DrMikeG/H2Remote/readme_img/h4remote.jpg

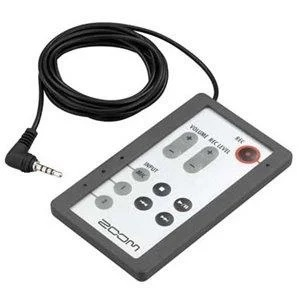
readme_img/h4remote.jpg
