DrMikeG/H2Remote/readme_img/pico01.jpg

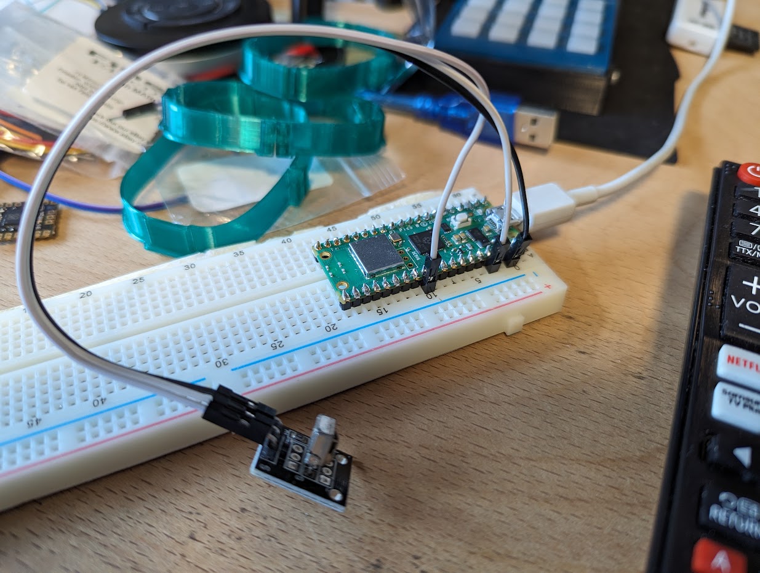
readme_img/pico01.jpg
