DrMikeG/H2Remote/readme_img/tiny_led_pins.png

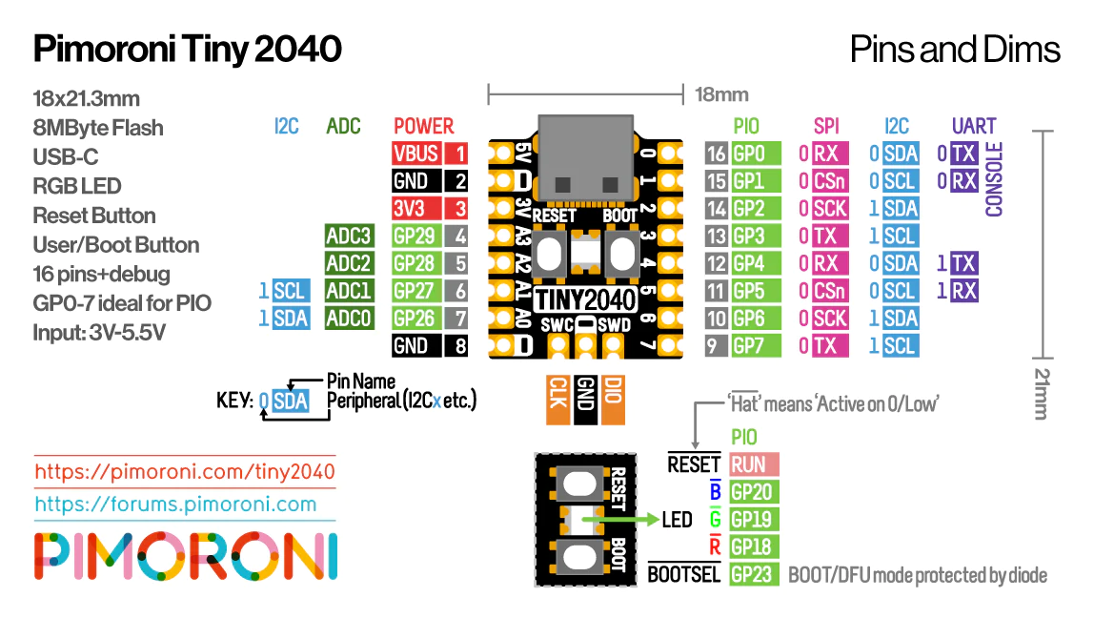
readme_img/tiny_led_pins.png
