DrMikeG/H2Remote/timelapse/pi3/Raspberry_Pi_7_Inch_Touchscreen_display_case_1585924/images/Raspi7inch_Split_Left_Case_SD_Access.jpg

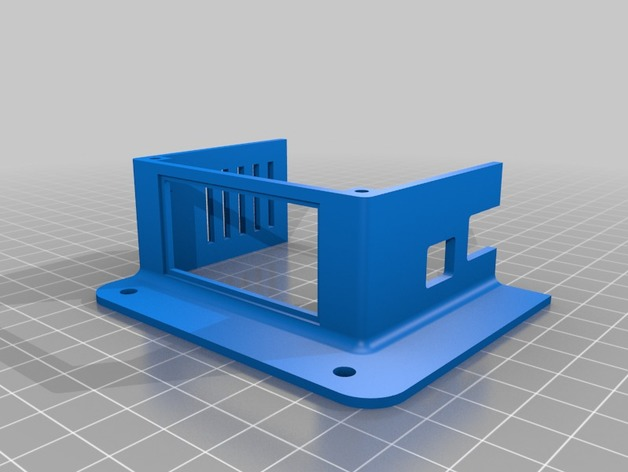
timelapse/pi3/Raspberry_Pi_7_Inch_Touchscreen_display_case_1585924/images/Raspi7inch_Split_Left_Case_SD_Access.jpg
