DrMikeG/H2Remote/Updates/Update1/00_Instant.png

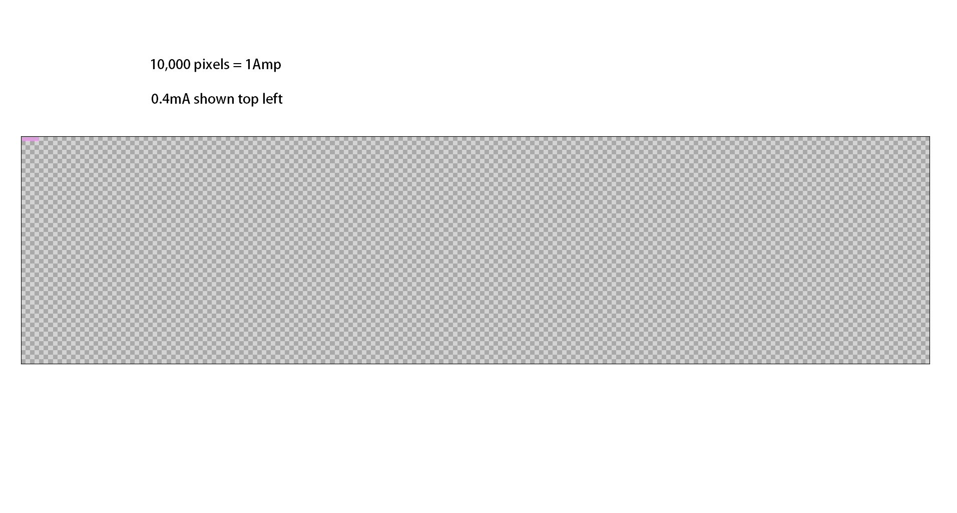
Updates/Update1/00_Instant.png
