DrMikeG/H2Remote/Updates/Update1/02_aas.png

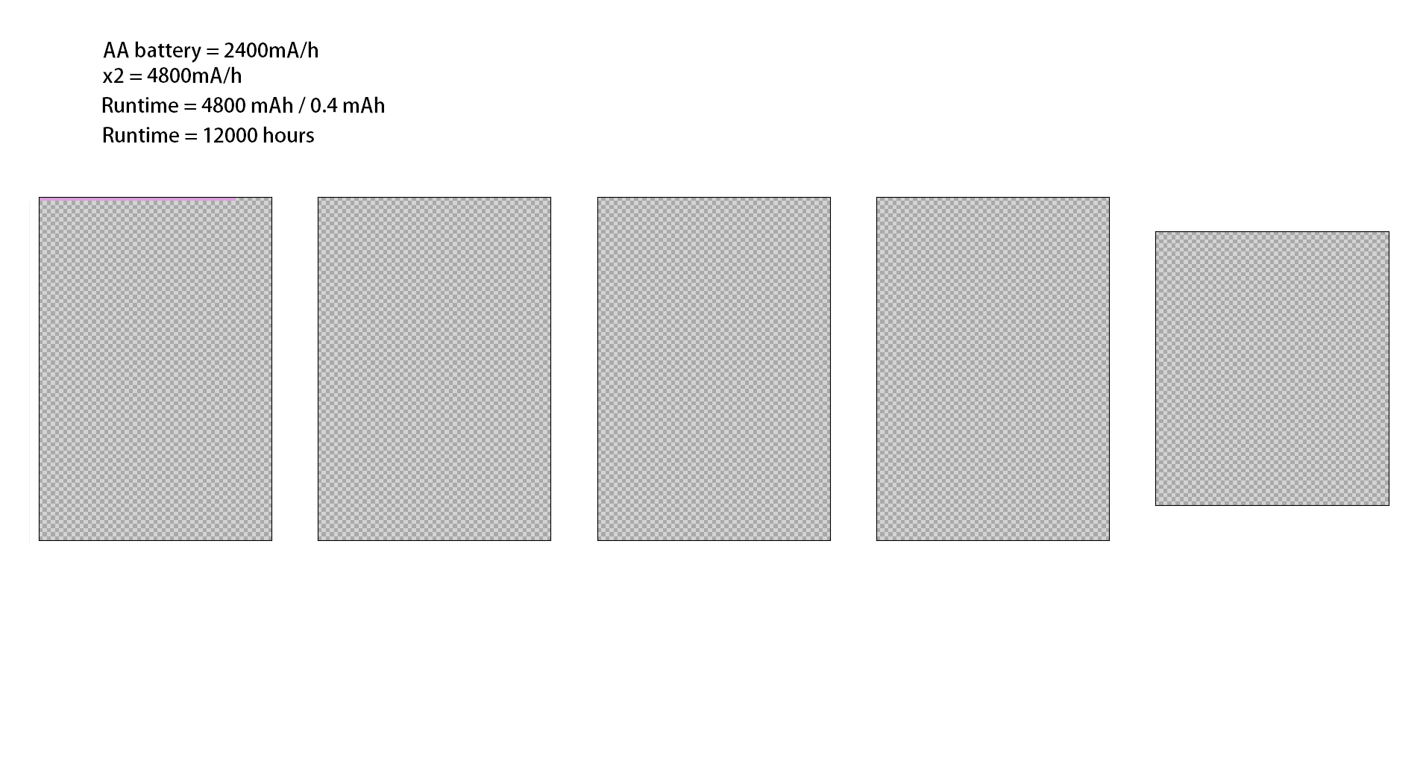
Updates/Update1/02_aas.png
