DrMikeG/H2Remote/parts/zeb/bouncy_base_02.stp

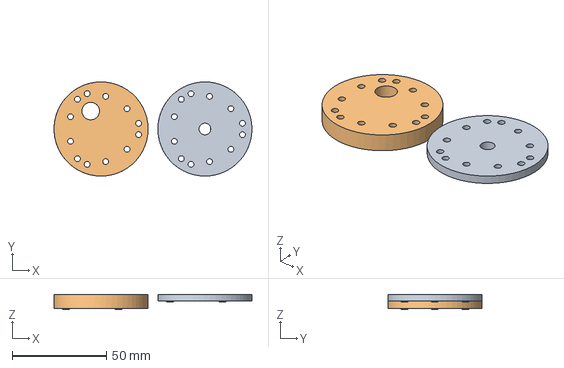
[picture p77: CAD file, 2023-07-23]
parts/zeb/bouncy_base_02.stp
105.2 x 50.0 x 8.00 mm
