DrMikeG/H2Remote/parts/mount_bucket/BaseCup_brim_02.stp

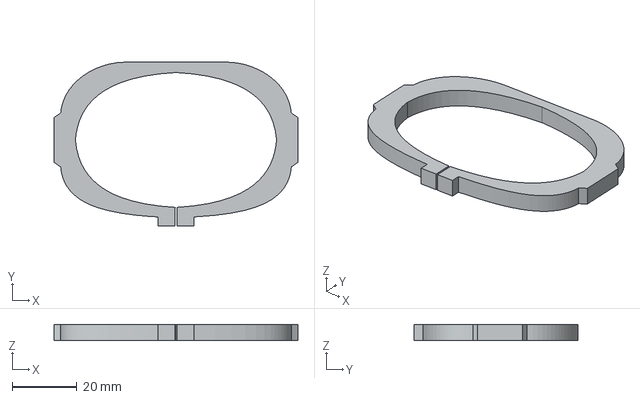
[picture p79: CAD file, 2023-07-16]
parts/mount_bucket/BaseCup_brim_02.stp
75.3 x 50.5 x 5.00 mm
