DrMikeG/H2Remote/parts/cr20/CaseFront_1.3mf

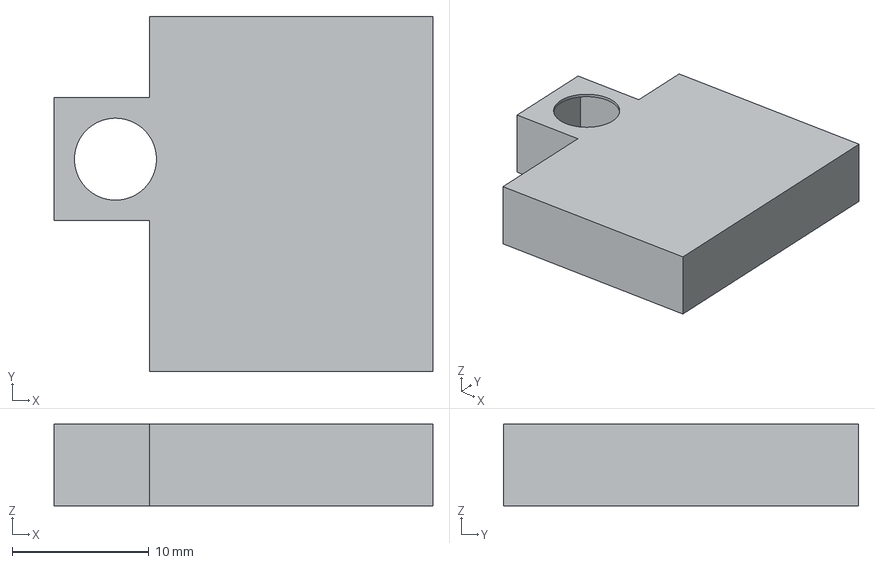
[picture p81: CAD file, 2023-08-12]
parts/cr20/CaseFront_1.3mf
27.8 x 26.0 x 6.00 mm
