DrMikeG/H2Remote/parts/zeb/bouncy_base_04.stp

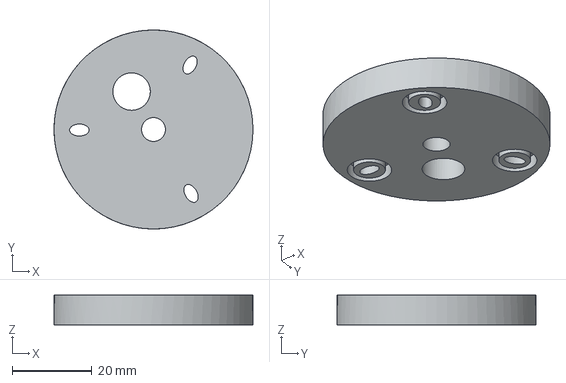
[picture p83: CAD file, 2023-07-23]
parts/zeb/bouncy_base_04.stp
50.0 x 50.0 x 7.50 mm
