DrMikeG/H2Remote/parts/cr20/CaseFront_0.3mf

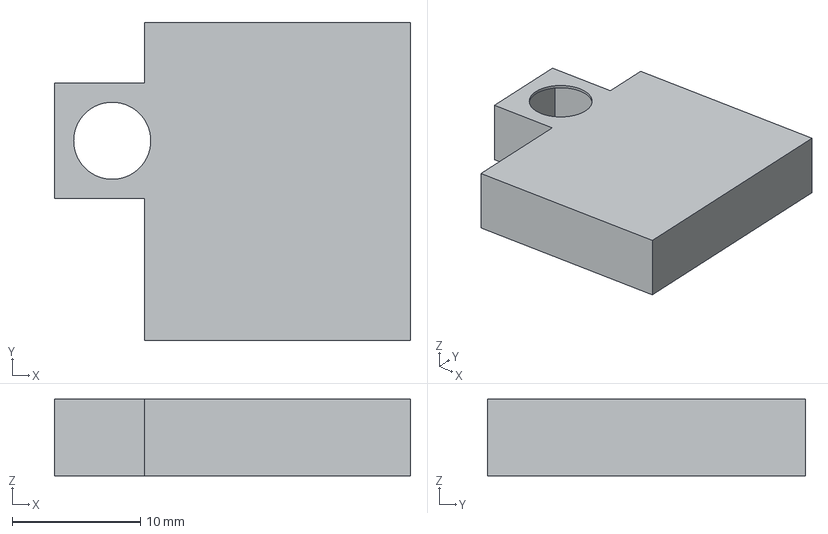
[picture p84: CAD file, 2023-08-12]
parts/cr20/CaseFront_0.3mf
27.8 x 24.8 x 6.00 mm
