DrMikeG/H2Remote/parts/zeb/slide03_x4.3mf

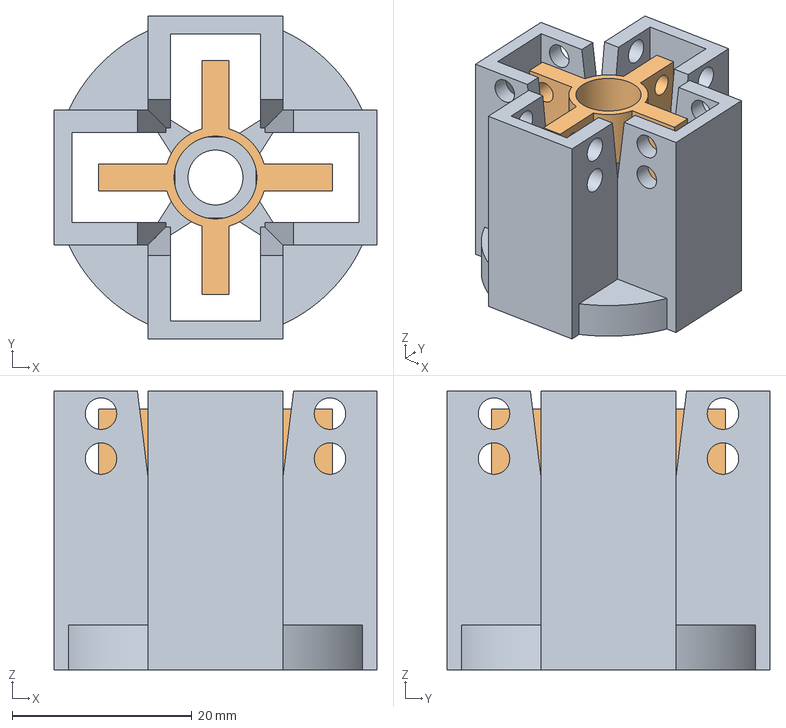
[picture p86: CAD file, 2023-07-23]
parts/zeb/slide03_x4.3mf
35.9 x 35.9 x 31.0 mm
slide03_x4 x 2
