DrMikeG/H2Remote/parts/cr20/CaseFront_3.3mf

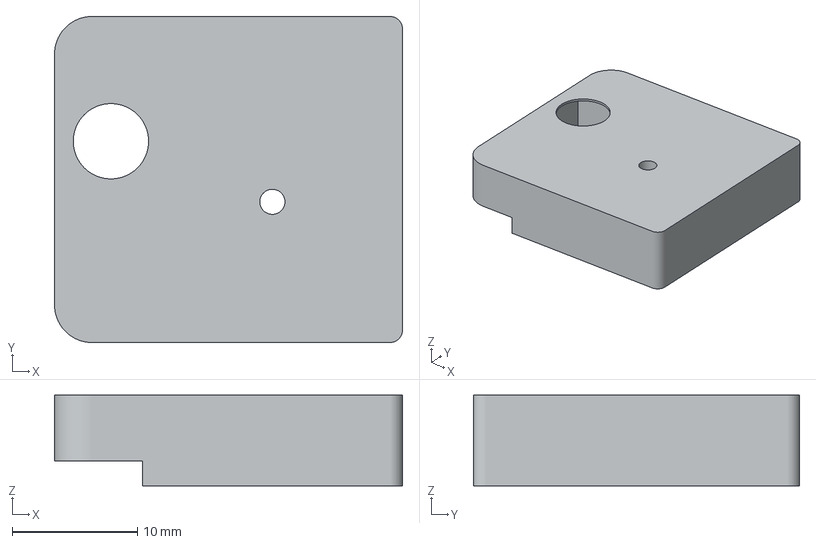
[picture p87: CAD file, 2023-08-12]
parts/cr20/CaseFront_3.3mf
27.8 x 26.0 x 7.25 mm
