DrMikeG/H2Remote/parts/FrameFor_RP2040_02.3mf

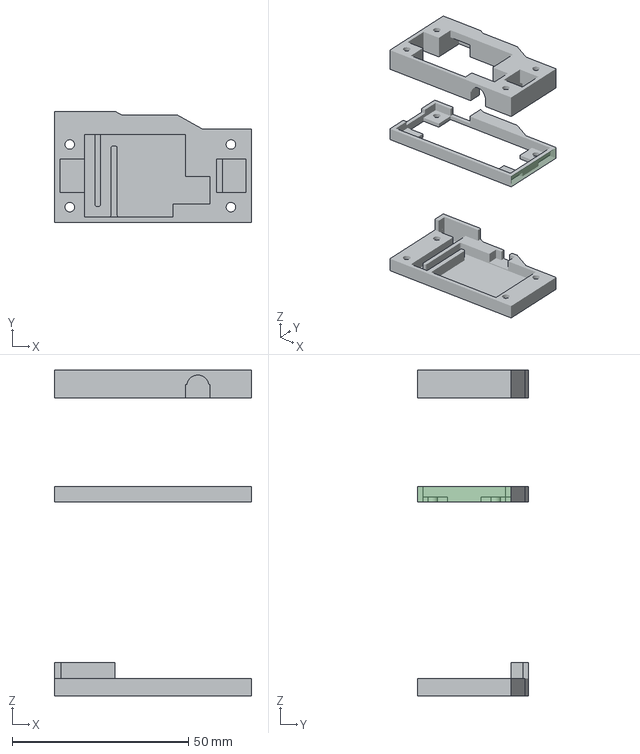
[picture p88: CAD file, 2023-08-06]
parts/FrameFor_RP2040_02.3mf
55.9 x 31.5 x 92.5 mm
FrameFor_RP2040_02 x 3
