DrMikeG/H2Remote/parts/mount_bucket/LowStrap_brim_01.stp

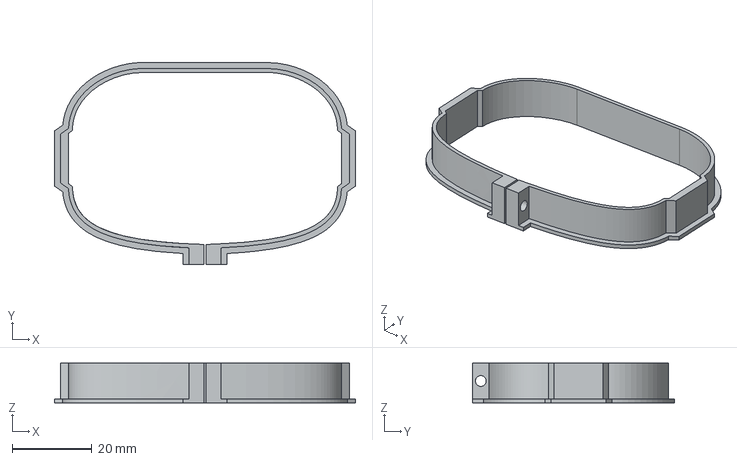
[picture p89: CAD file, 2023-07-16]
parts/mount_bucket/LowStrap_brim_01.stp
75.3 x 50.5 x 10.0 mm
