DrMikeG/H2Remote/parts/zeb/slide01_x4.3mf

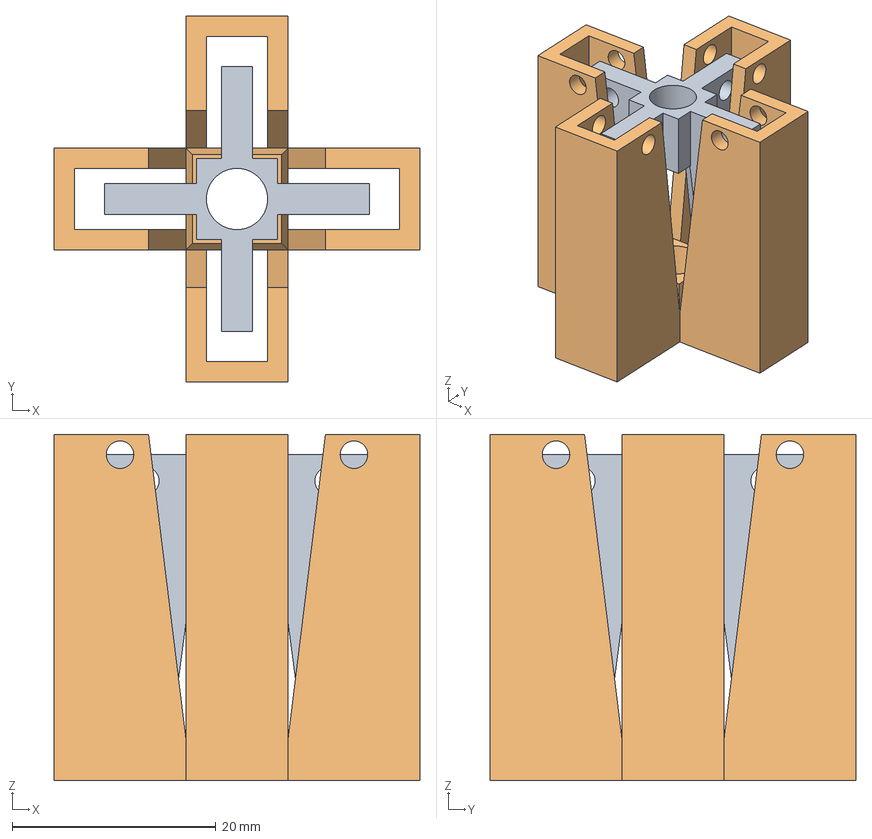
[picture p90: CAD file, 2023-07-18]
parts/zeb/slide01_x4.3mf
35.9 x 35.9 x 34.0 mm
slide01_x4 x 2
