DrMikeG/H2Remote/timelapse/pi3/Raspberry_Pi_7_Inch_Touchscreen_display_case_1585924/files/Raspi7inch_Front_Split_Left.stl

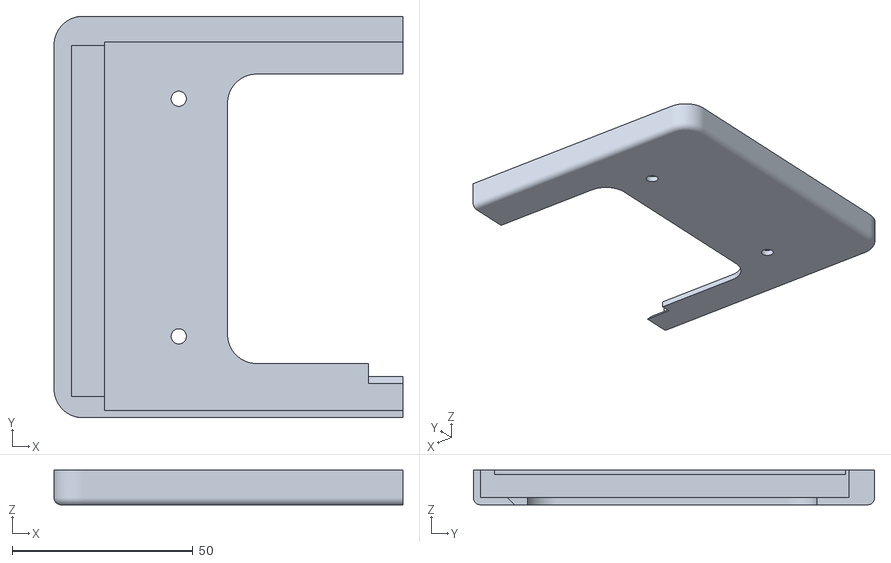
[picture p91: CAD file, 2023-07-14]
timelapse/pi3/Raspberry_Pi_7_Inch_Touchscreen_display_case_1585924/files/Raspi7inch_Front_Split_Left.stl
96.5 x 111.0 x 9.60
