DrMikeG/H2Remote/parts/cr20/CaseFront_2.3mf

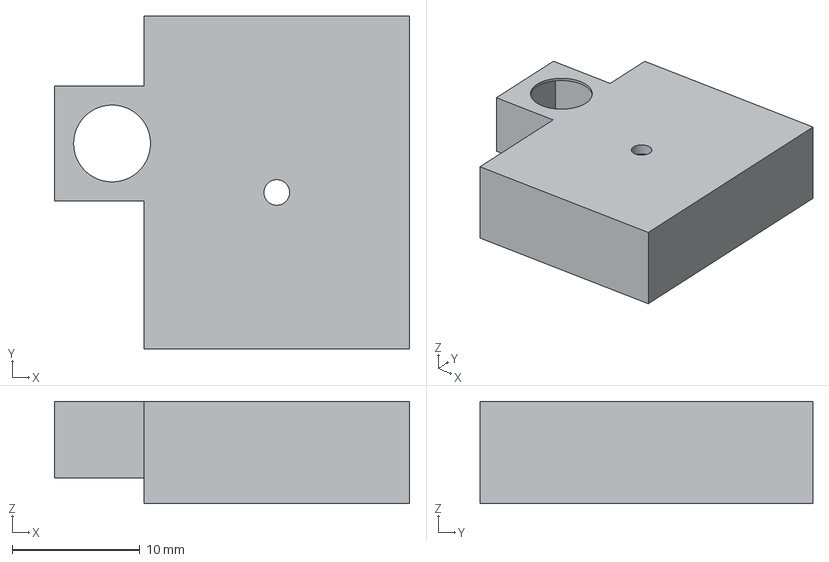
[picture p92: CAD file, 2023-08-12]
parts/cr20/CaseFront_2.3mf
27.8 x 26.0 x 8.00 mm
