DrMikeG/H2Remote/parts/zeb/slide02_x4.3mf

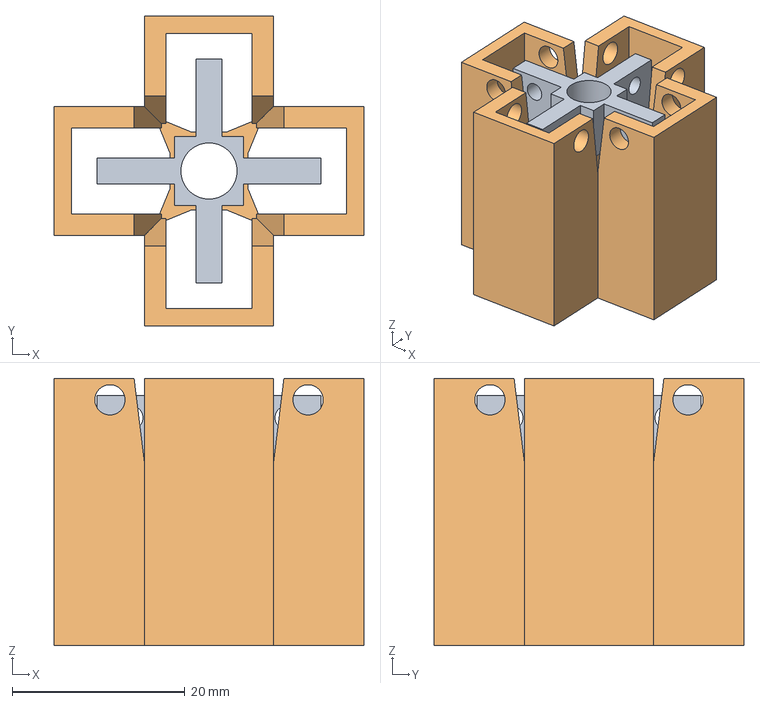
[picture p93: CAD file, 2023-07-18]
parts/zeb/slide02_x4.3mf
35.9 x 35.9 x 31.0 mm
slide02_x4 x 2
