DrMikeG/H2Remote/timelapse/pi3/Raspberry_Pi_7_Inch_Touchscreen_display_case_1585924/files/Raspi7inch_Case_SD_Access.stl

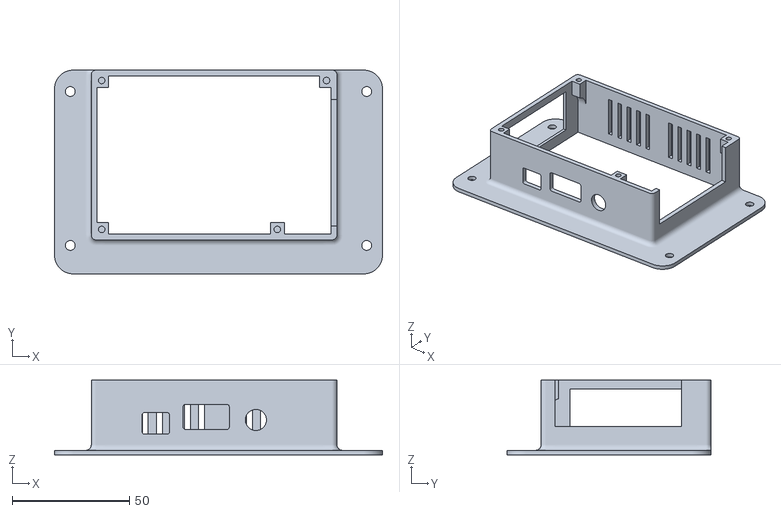
[picture p94: CAD file, 2023-07-14]
timelapse/pi3/Raspberry_Pi_7_Inch_Touchscreen_display_case_1585924/files/Raspi7inch_Case_SD_Access.stl
140.0 x 87.0 x 32.0
