DrMikeG/H2Remote/parts/FrameFor_RP2040_00.3mf

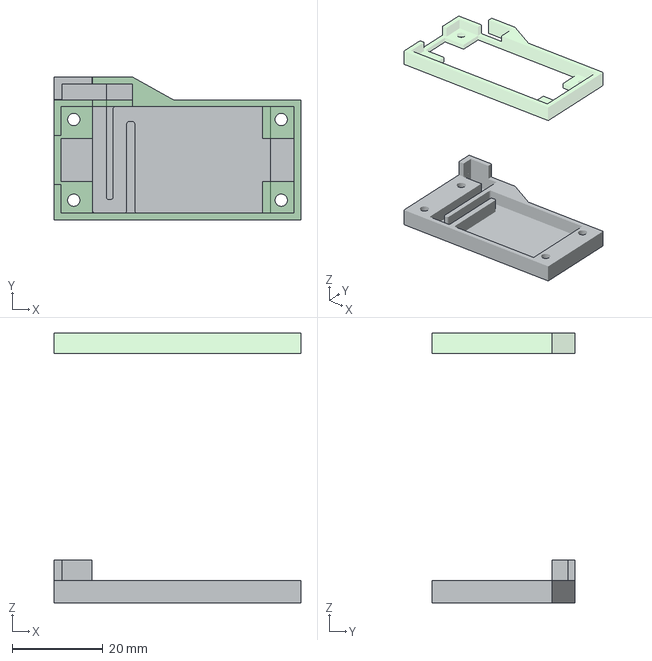
[picture p95: CAD file, 2023-08-04]
parts/FrameFor_RP2040_00.3mf
54.4 x 31.5 x 59.5 mm
FrameFor_RP2040_00 x 2
