DrMikeG/H2Remote/parts/mount_bucket/Bucket_01.stp

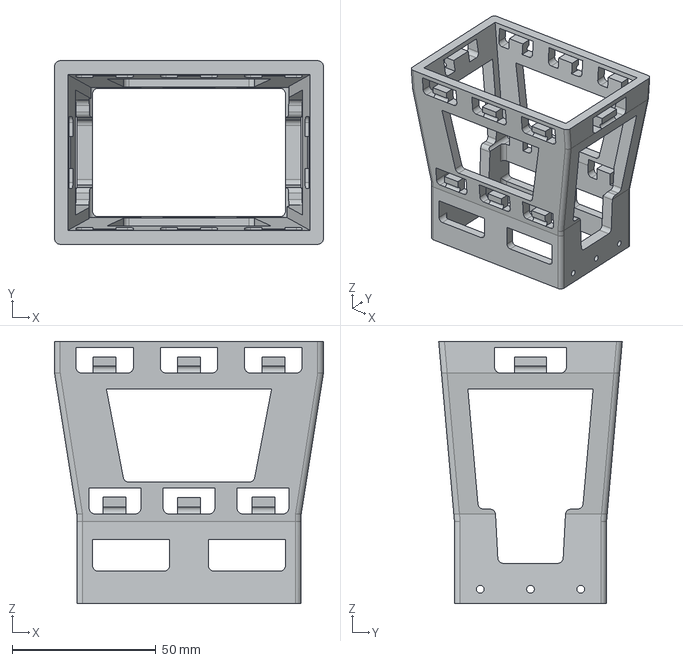
[picture p96: CAD file, 2023-07-16]
parts/mount_bucket/Bucket_01.stp
93.7 x 63.9 x 91.3 mm
