DrMikeG/H2Remote/parts/zeb/bouncy_base_01.stp

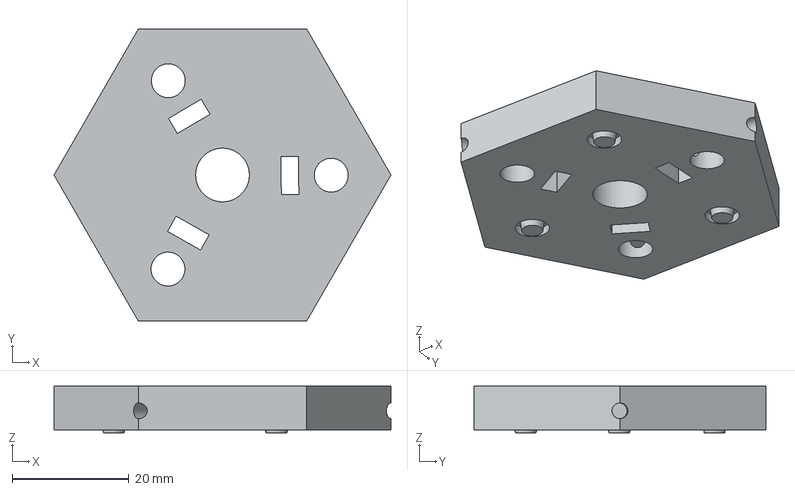
[picture p97: CAD file, 2023-07-17]
parts/zeb/bouncy_base_01.stp
57.7 x 50.0 x 8.00 mm
