DrMikeG/H2Remote/parts/FrameFor_RP2040_01.3mf

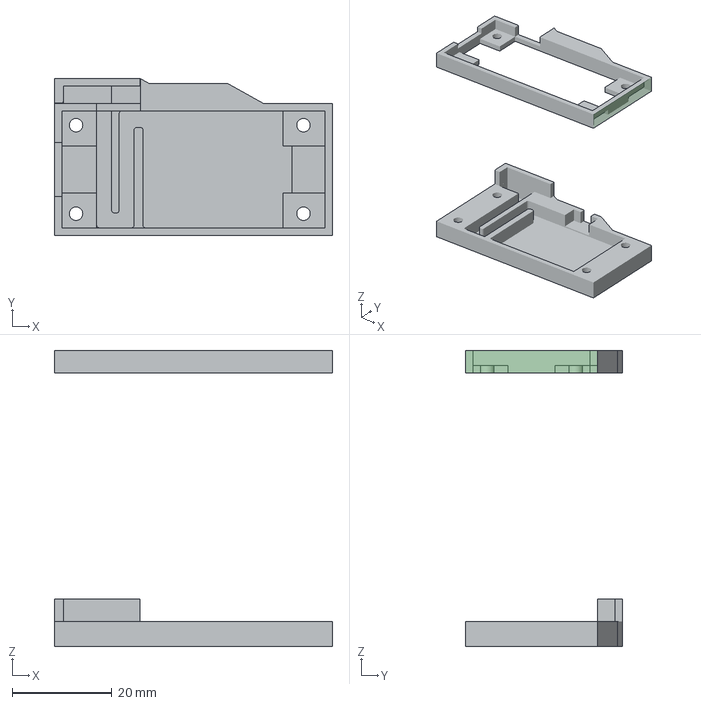
[picture p98: CAD file, 2023-08-04]
parts/FrameFor_RP2040_01.3mf
55.9 x 31.5 x 59.5 mm
FrameFor_RP2040_01 x 2
