DrMikeG/H2Remote/parts/mount_bucket/LowStrap_01.stp

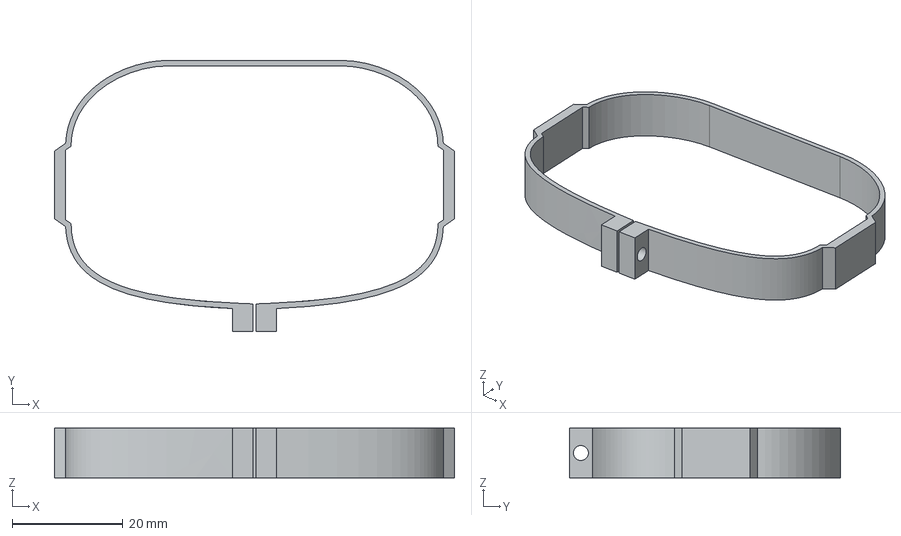
[picture p99: CAD file, 2023-07-16]
parts/mount_bucket/LowStrap_01.stp
72.3 x 49.0 x 9.00 mm
