DrMikeG/H2Remote/timelapse/pi3/Raspberry_Pi_7_Inch_Touchscreen_display_case_1585924/files/Raspi7inch_Front.stl

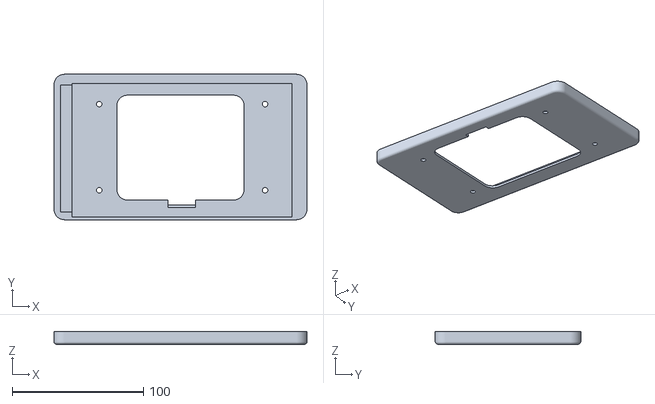
[picture p100: CAD file, 2023-07-14]
timelapse/pi3/Raspberry_Pi_7_Inch_Touchscreen_display_case_1585924/files/Raspi7inch_Front.stl
193.0 x 111.0 x 9.60
