DrMikeG/H2Remote/parts/mount_bucket/makeImageCached (1).jpg

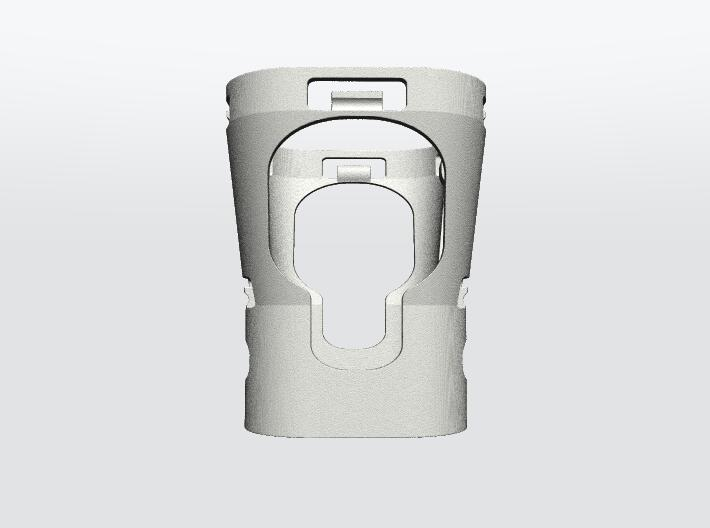
parts/mount_bucket/makeImageCached (1).jpg
