DrMikeG/H2Remote/parts/mount_bucket/makeImageCached (2).jpg

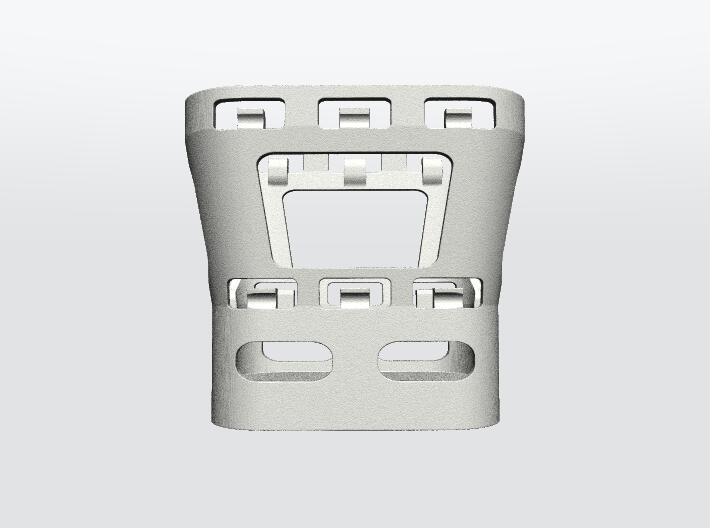
parts/mount_bucket/makeImageCached (2).jpg
