DrMikeG/H2Remote/parts/mount_bucket/makeImageCached (4).jpg

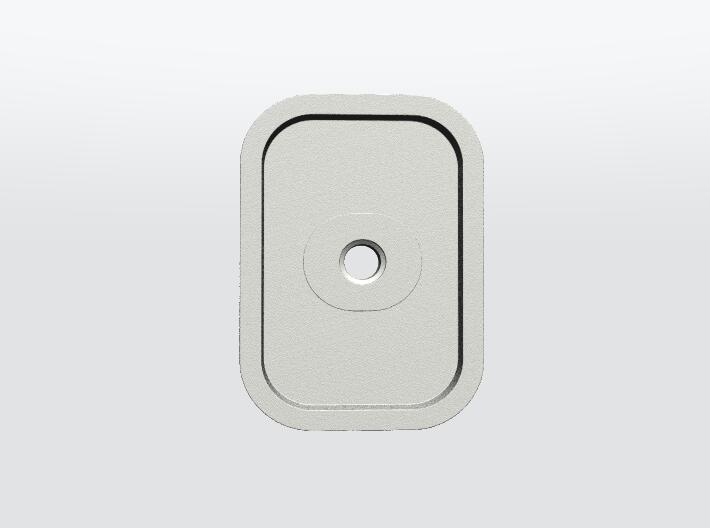
parts/mount_bucket/makeImageCached (4).jpg
