DrMikeG/H2Remote/parts/mount_bucket/makeImageCached (5).jpg

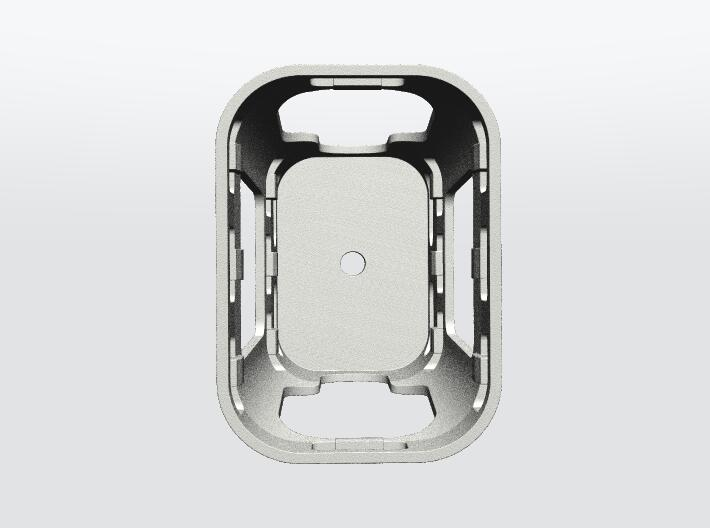
parts/mount_bucket/makeImageCached (5).jpg
