DrMikeG/H2Remote/timelapse/camera/capture.py

#!/usr/bin/python3

# Capture a JPEG while still running in the preview mode.

import time

from picamera2 import Picamera2, Preview

picam2 = Picamera2()

capture_config = picam2.create_still_configuration()

picam2.start()
time.sleep(2)

picam2.switch_mode_and_capture_file(capture_config, "/home/timelapse/Pictures/capture.jpg")
