DrMikeG/H2Remote/06_pico_pio/blink.py

import board
import digitalio
import time

led = digitalio.DigitalInOut(board.GP15)
led.direction = digitalio.Direction.OUTPUT

while True:
    print("Hello, CircuitPython!")
    led.value = True
    time.sleep(1)
    led.value = False
    time.sleep(1)


# The Pico W does not have an LED connected to a GPIO.
# So I have manually added one on GP15 (bottom left row)
